cwill713/Software-Defined-Radio/Pictures/Arduino and Si5351.jpg

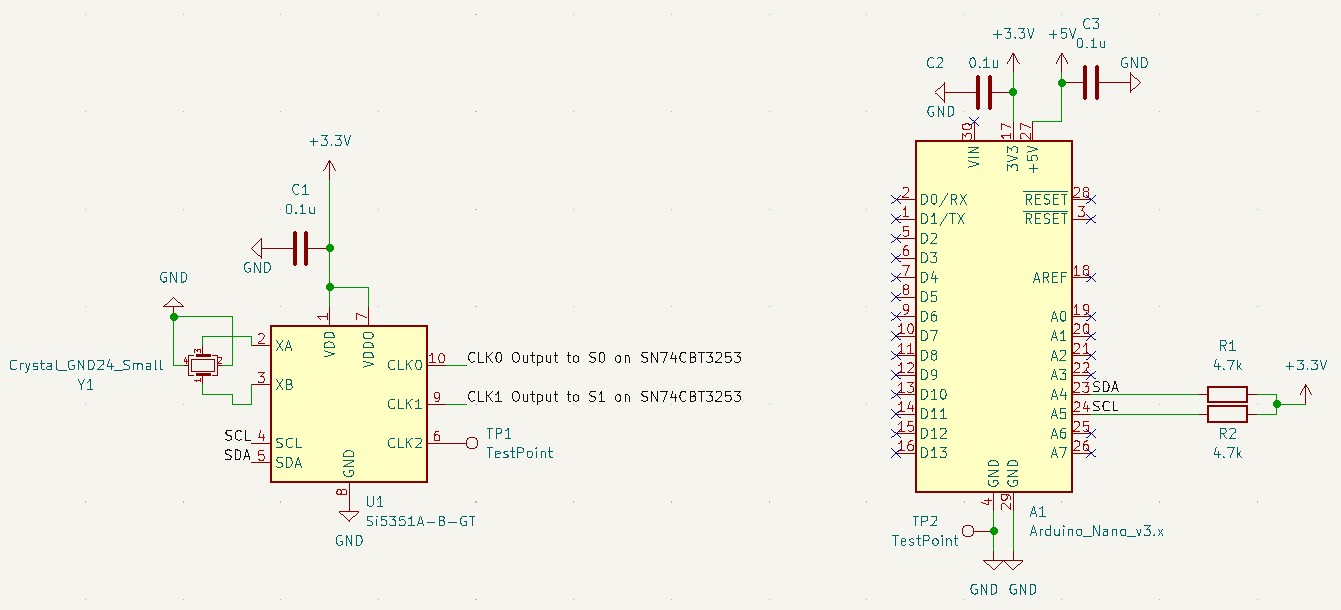
Pictures/Arduino and Si5351.jpg
