cwill713/Software-Defined-Radio/Pictures/BandPass Filter and Voltage Divider.jpg

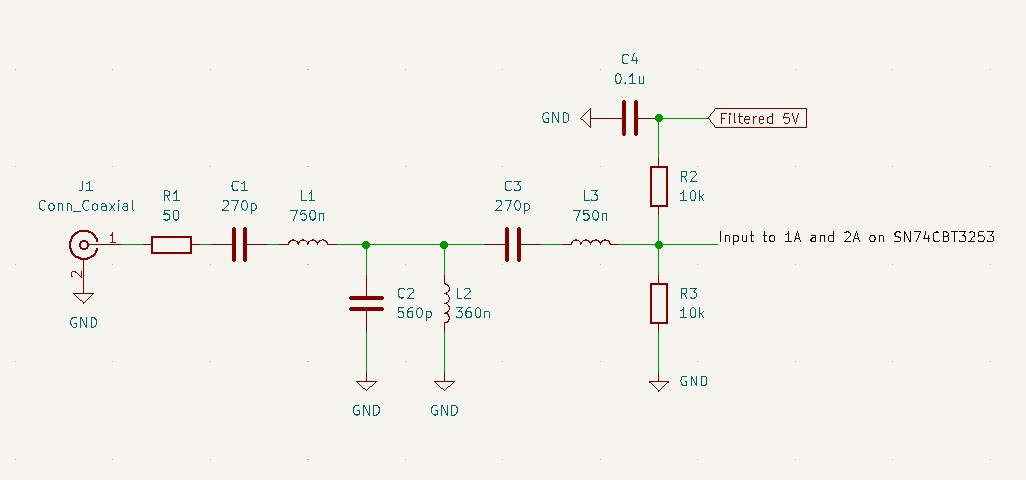
Pictures/BandPass Filter and Voltage Divider.jpg
