cwill713/Software-Defined-Radio/Pictures/Bandpass Filter Simulation Graph.jpg

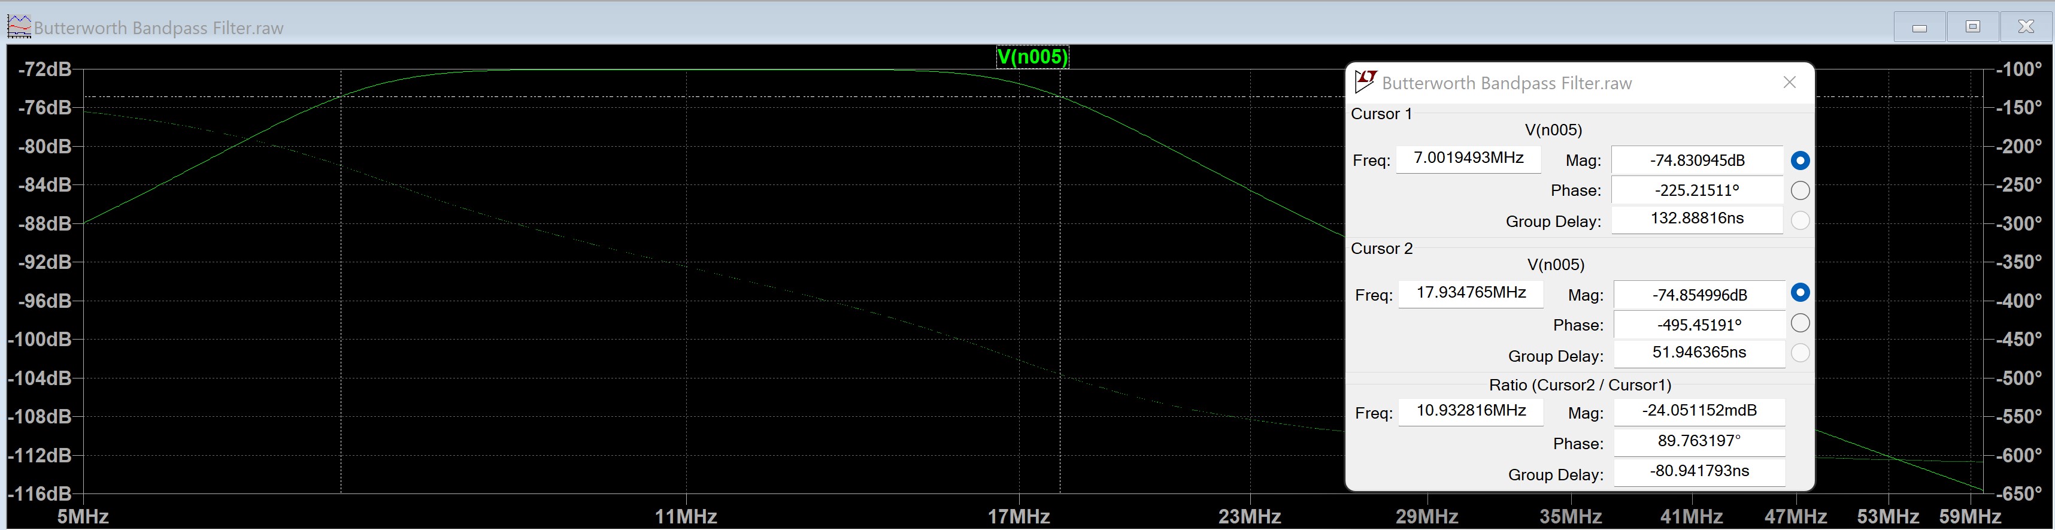
Pictures/Bandpass Filter Simulation Graph.jpg
