cwill713/Software-Defined-Radio/Pictures/Bandpass Filter Simulation.jpg

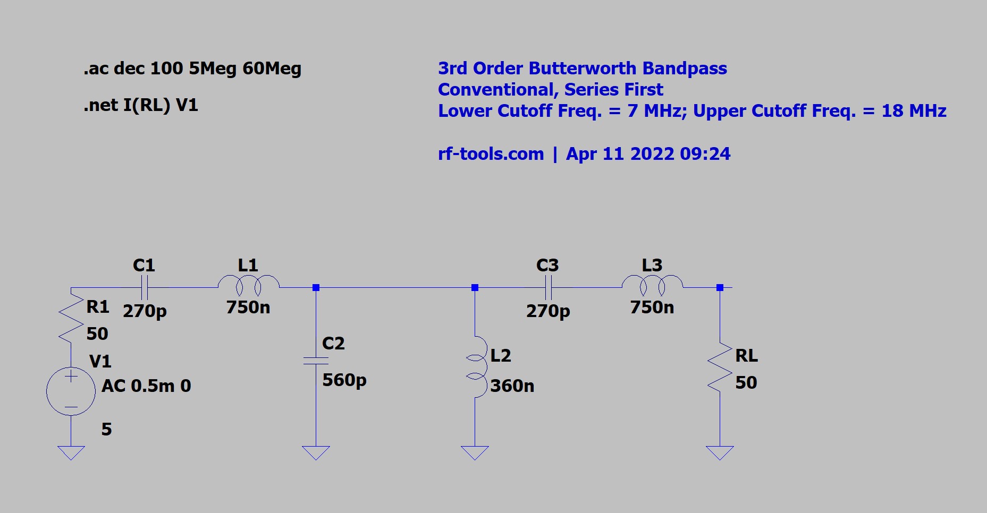
Pictures/Bandpass Filter Simulation.jpg
