cwill713/Software-Defined-Radio/Pictures/Complete SDR Simulation.jpg

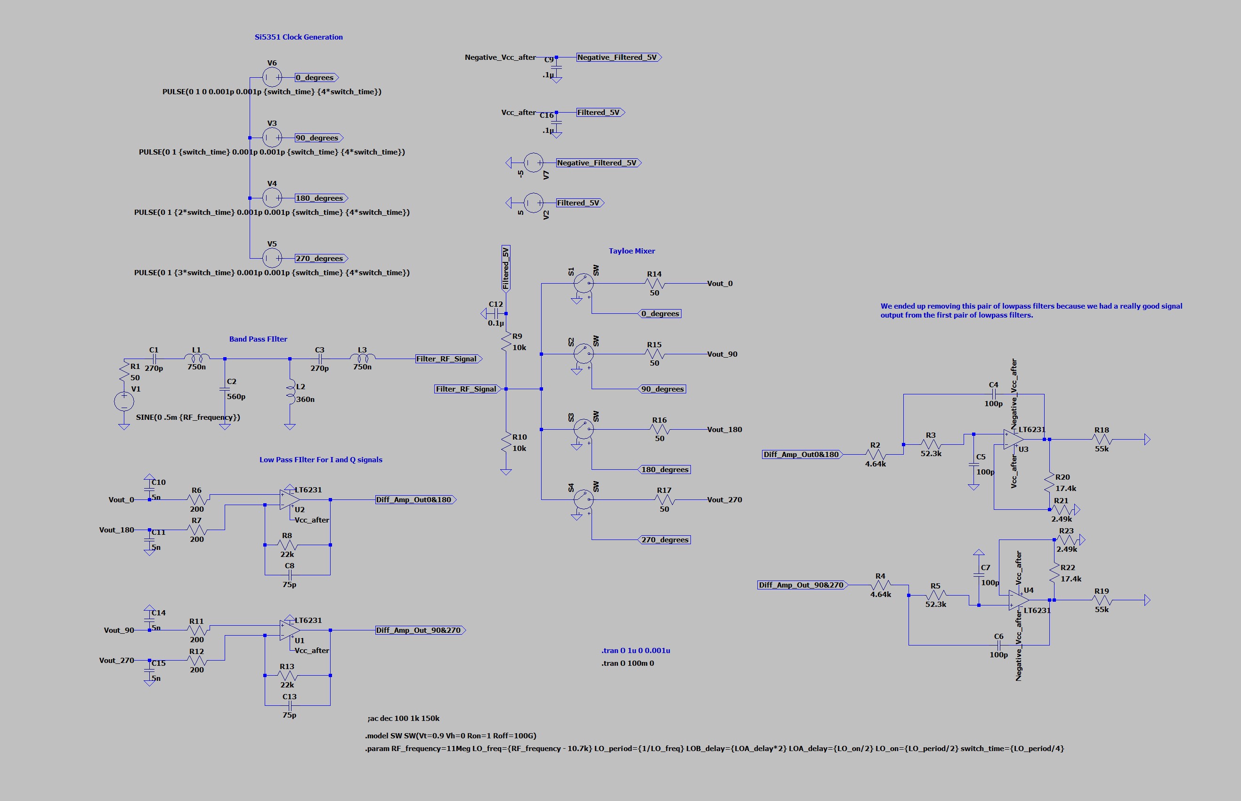
Pictures/Complete SDR Simulation.jpg
