cwill713/Software-Defined-Radio/Pictures/Complete Simulation Graph.jpg

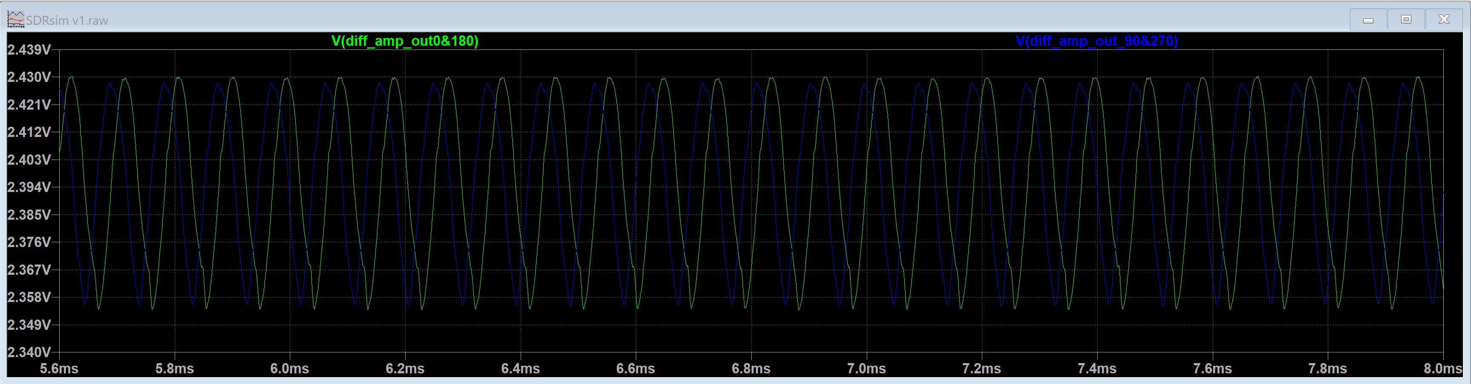
Pictures/Complete Simulation Graph.jpg
