cwill713/Software-Defined-Radio/Pictures/Josh's Fixed Board image 1.jpg

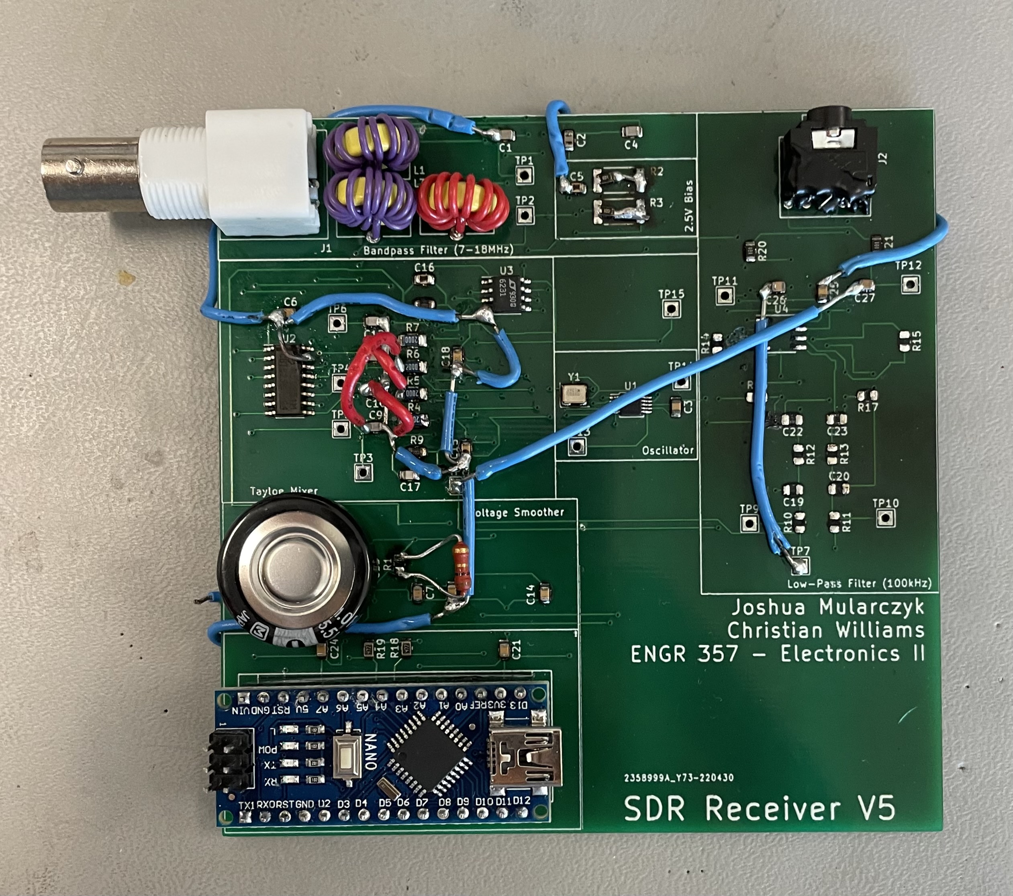
Pictures/Josh's Fixed Board image 1.jpg
