cwill713/Software-Defined-Radio/Pictures/Josh's Fixed Board image 3.jpg

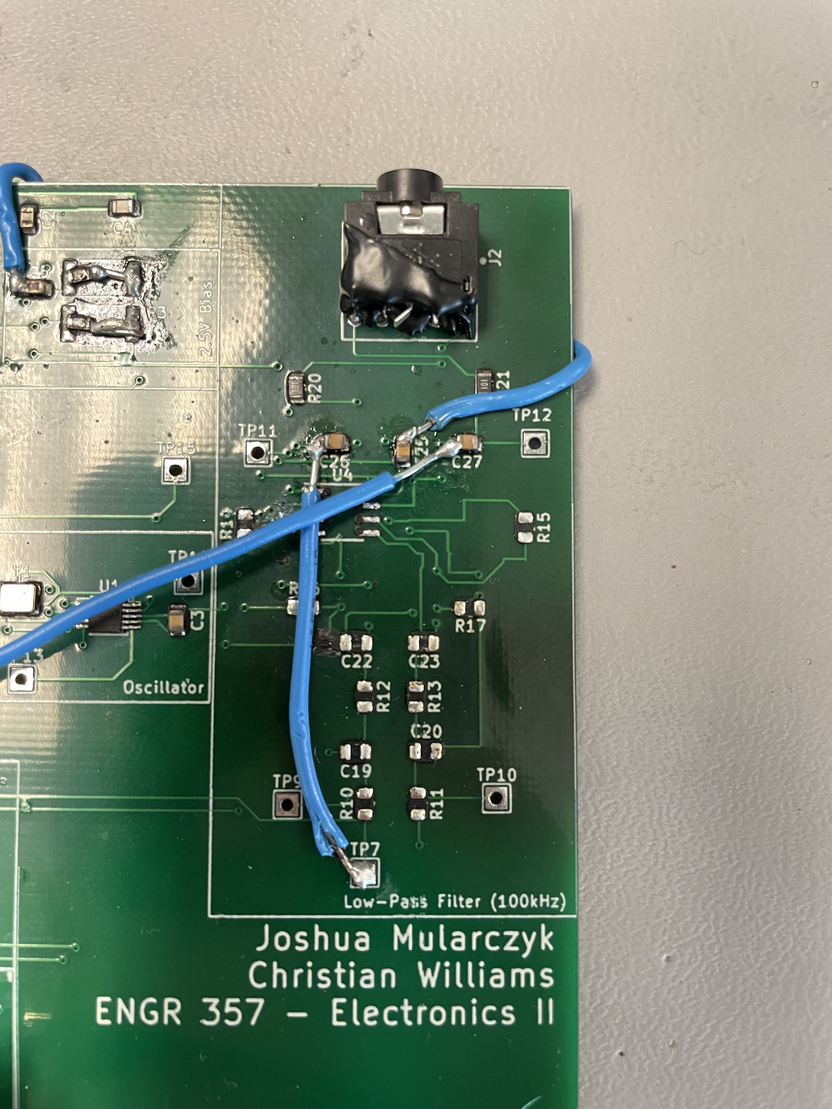
Pictures/Josh's Fixed Board image 3.jpg
