cwill713/Software-Defined-Radio/Pictures/listeningIn.png

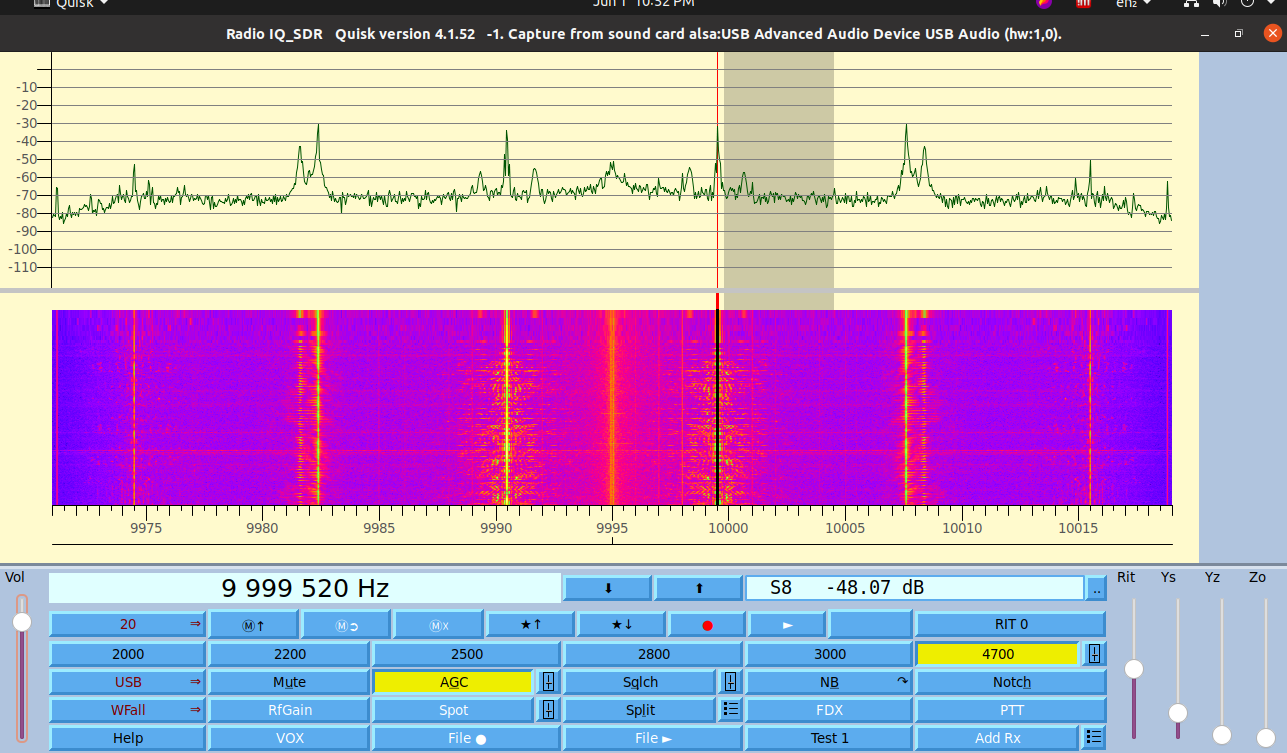
Pictures/listeningIn.png
