cwill713/Software-Defined-Radio/Pictures/LowPass Filter Simulation.jpg

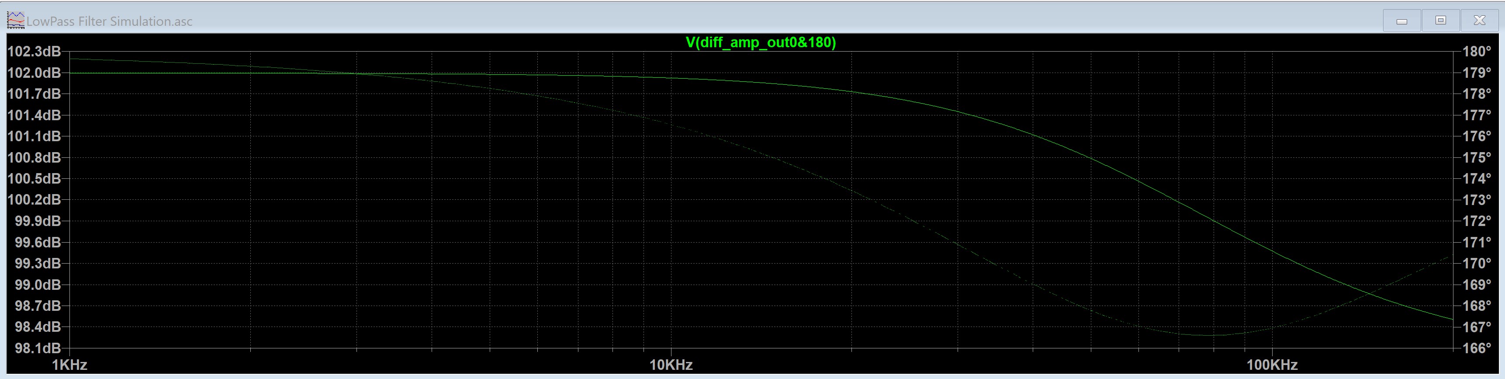
Pictures/LowPass Filter Simulation.jpg
