cwill713/Software-Defined-Radio/Pictures/minDec.png

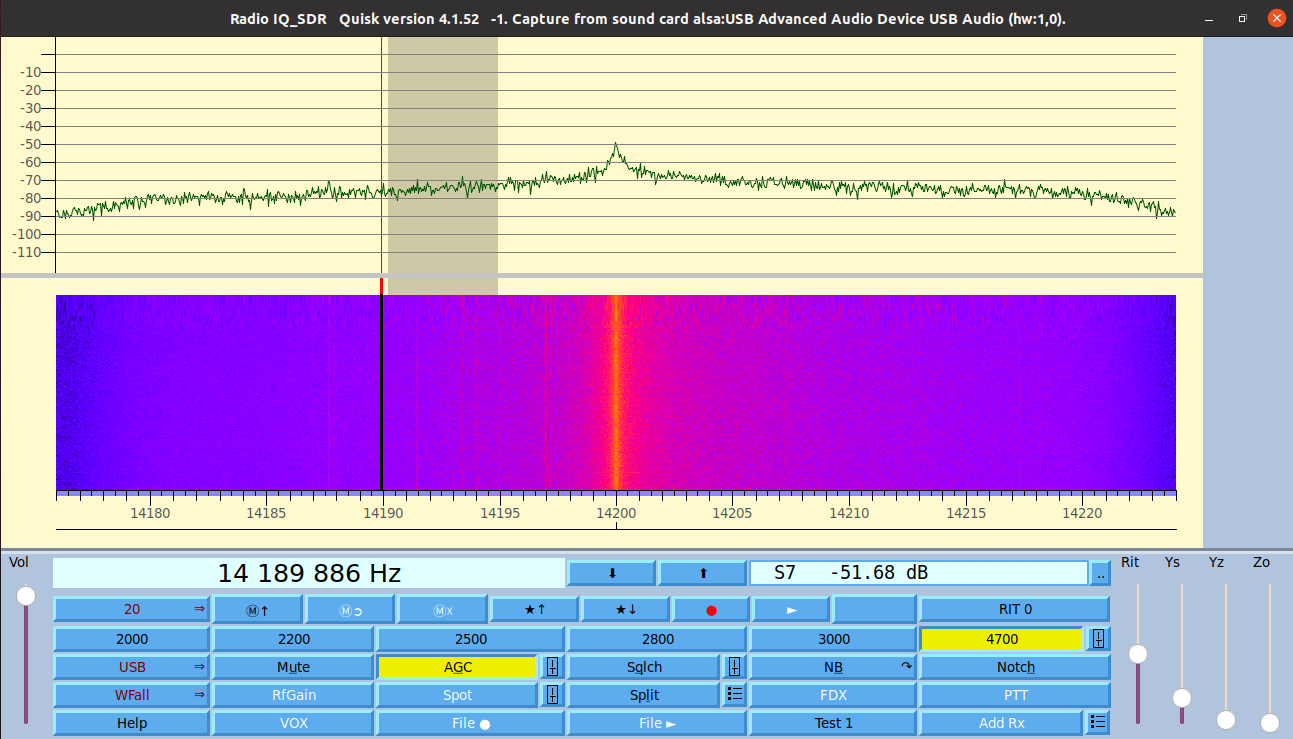
Pictures/minDec.png
