cwill713/Software-Defined-Radio/Pictures/Tayloe Mixer.jpg

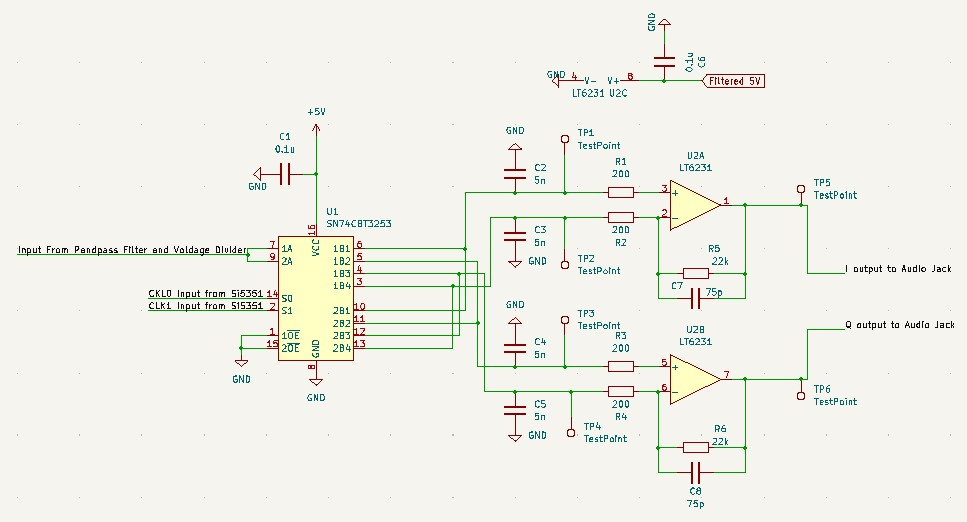
Pictures/Tayloe Mixer.jpg
