cwill713/Software-Defined-Radio/Pictures/V5 Circuit Board.jpg

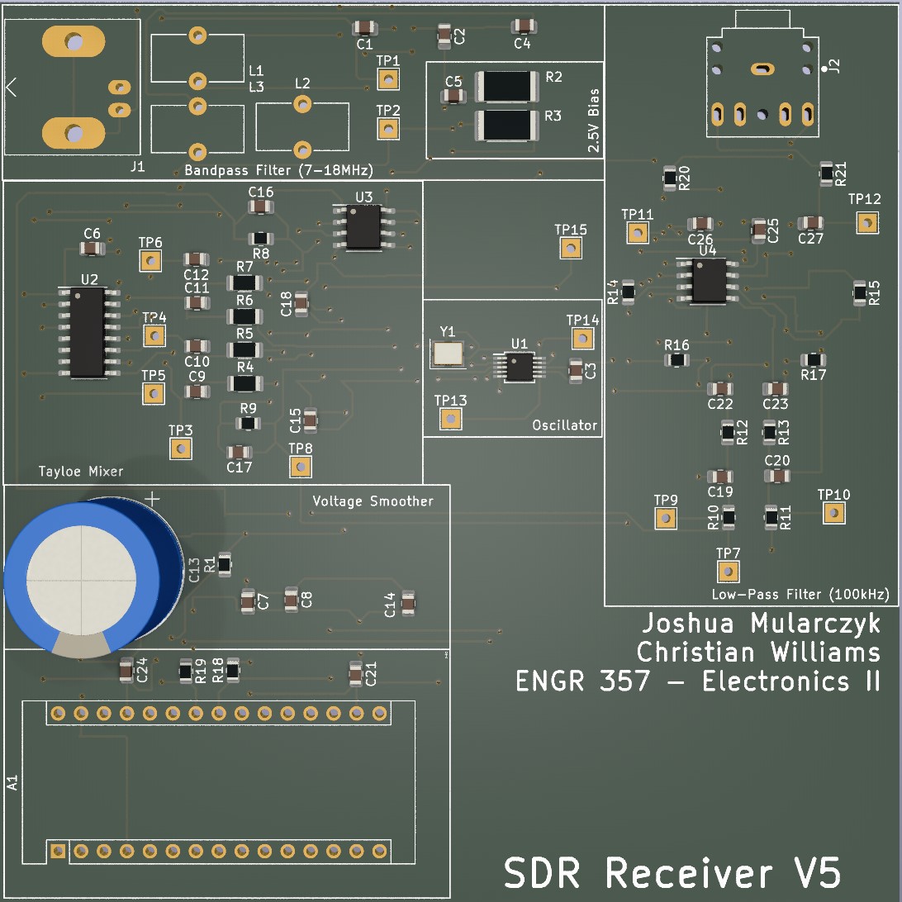
Pictures/V5 Circuit Board.jpg
