cwill713/Software-Defined-Radio/Pictures/Voltage Smoother.jpg

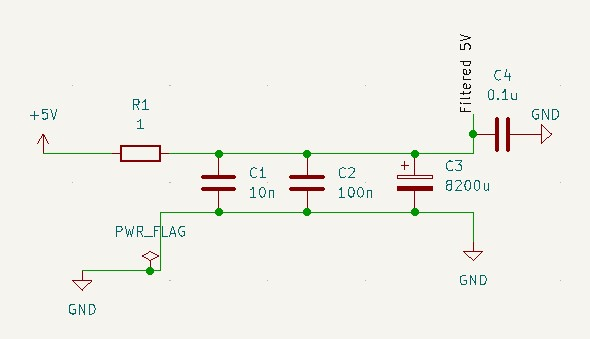
Pictures/Voltage Smoother.jpg
