cwill713/Software-Defined-Radio/Pictures/weather.png

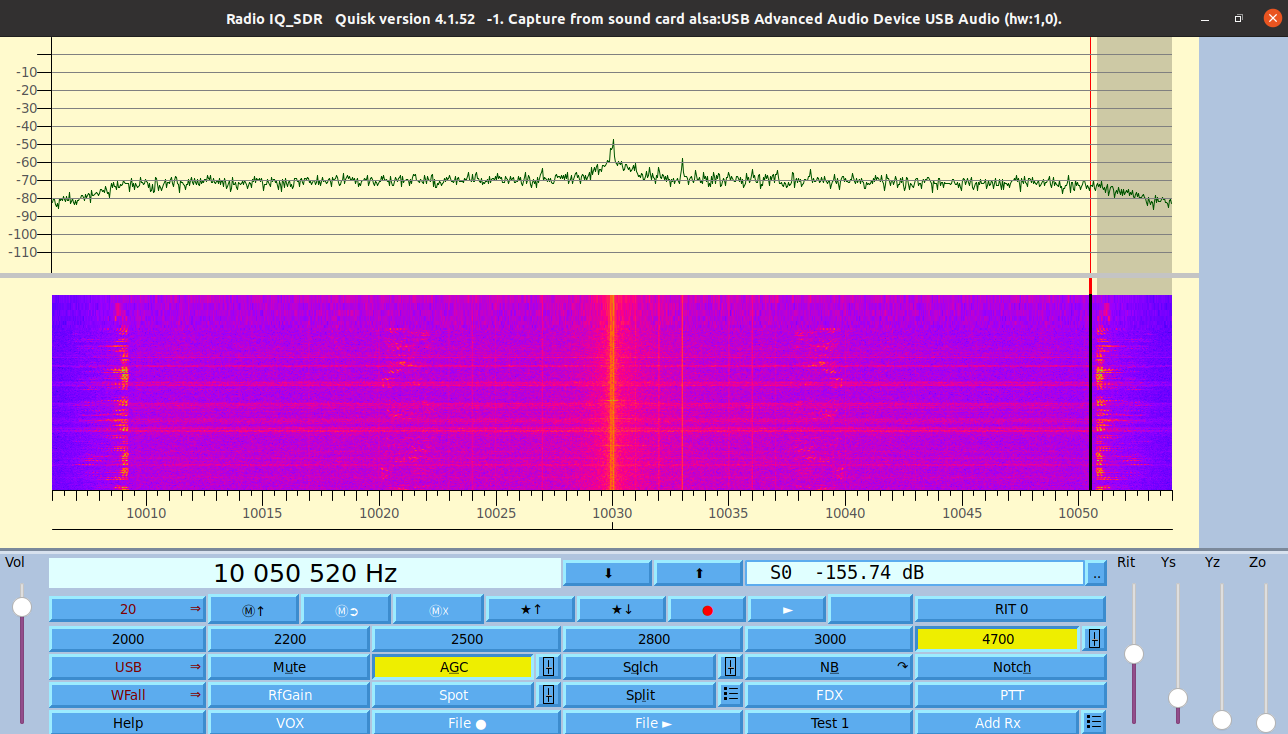
Pictures/weather.png
