cwill713/Software-Defined-Radio/Schematic Files/SDRrecV5/PDFFilesV5/Complete Schematic V4-F_Mask.pdf

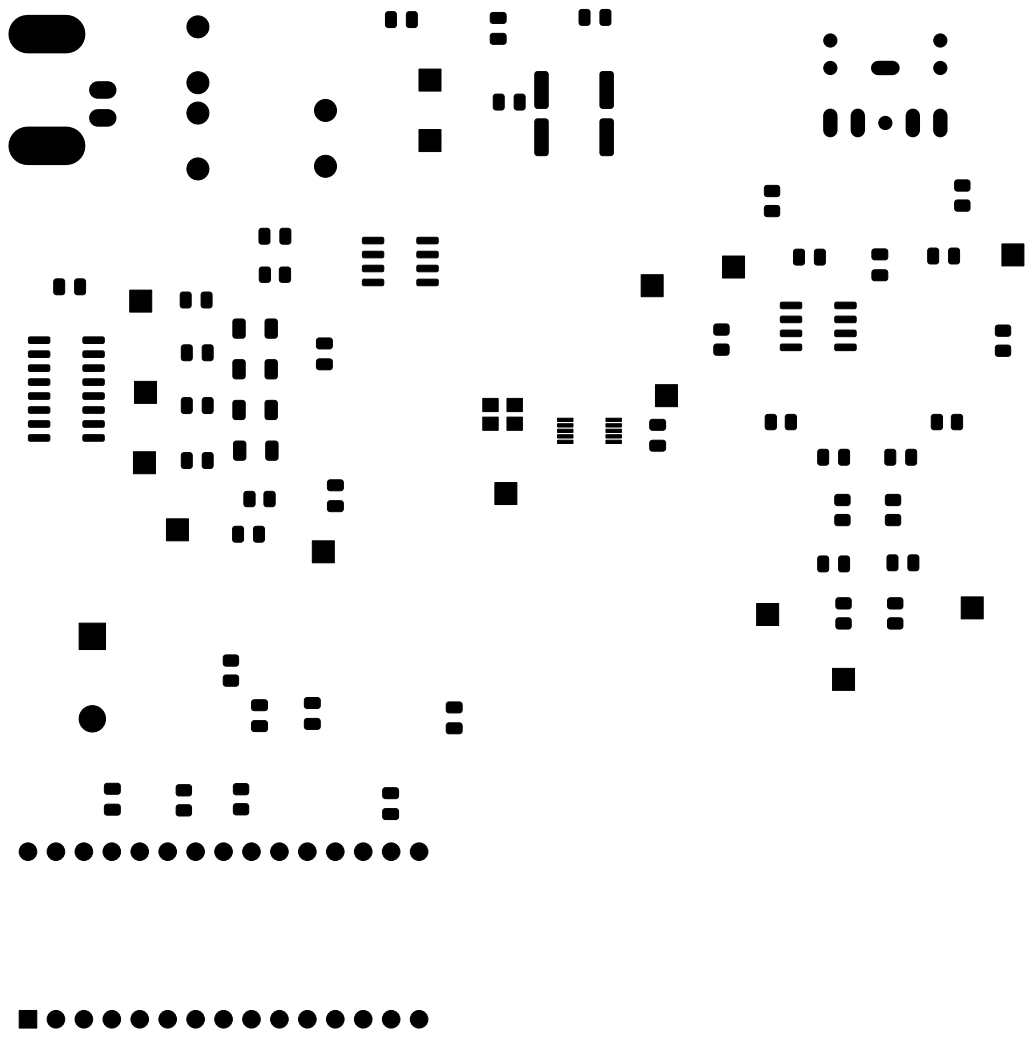
[picture p34: page 1]
