cwill713/Software-Defined-Radio/Schematic Files/SDRrecV5/PDFFilesV5/Complete Schematic V4-F_Silkscreen.pdf

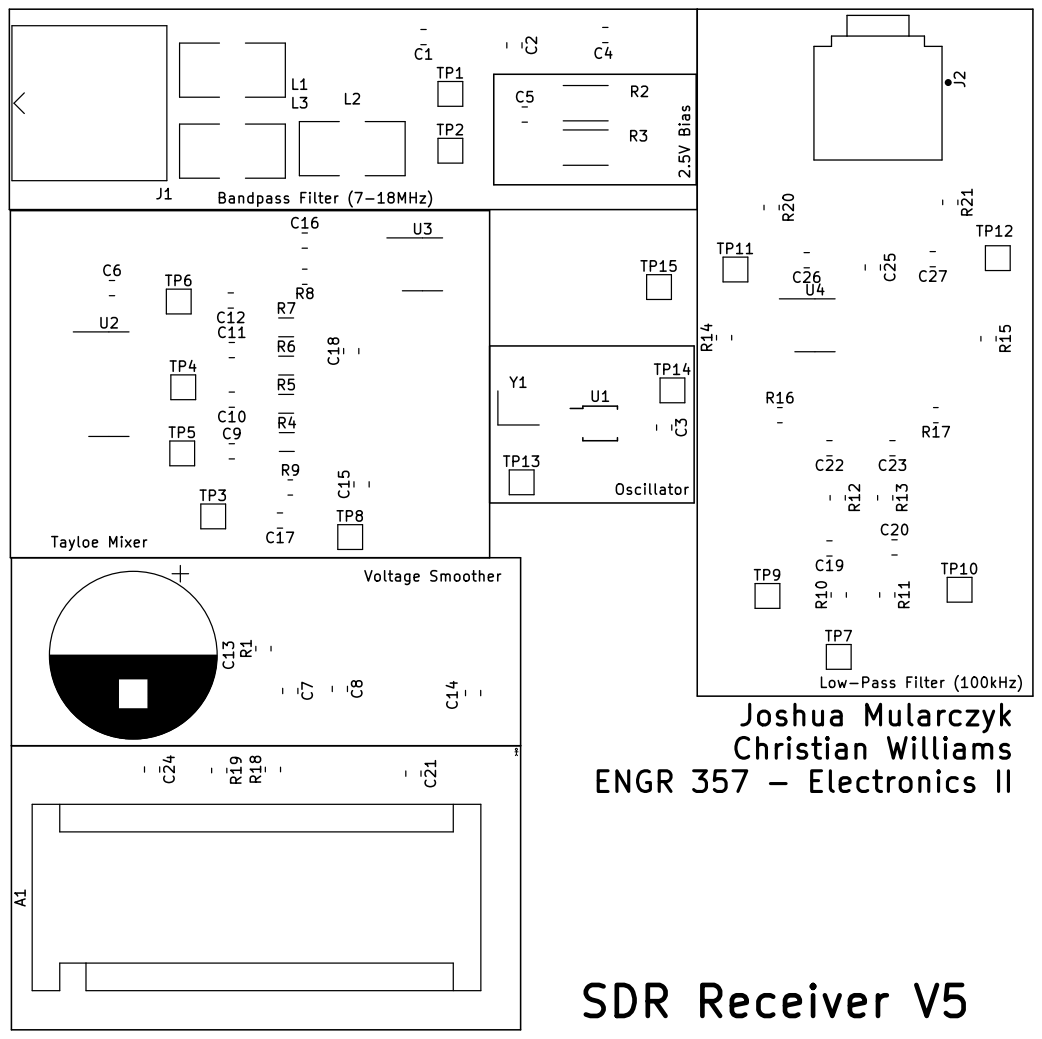
[picture p35: page 1]
