cwill713/Software-Defined-Radio/Simulation Files/LowPass Filter Simulation.asc

C1: cap; 75p
C2: cap; 5n
C3: cap; 5n
R1: res; 200
R2: res; 200
R3: res; 22k
U1: LT6231
V1: voltage; ""; AC 200k 0
V2: voltage; ""; AC 200k 180
Named nets: 0, Vout_0, Vout_180, Vcc_after, Diff_Amp_Out0&180
Low Pass FIlter For I and Q signals
.ac dec 100 1k 200k
