cwill713/Software-Defined-Radio/Simulation Files/Noise Simulation.asc

C1: cap; 5n
C2: cap; 5n
C3: cap; 5n
C4: cap; 75p
C5: cap; 75p
C6: cap; .1µ
C7: cap; 5n
R1: res; 200
R2: res; 200
R3: res; 22k
R4: res; 200
R5: res; 200
R6: res; 22k
R8: res; 55k
R9: res; 10k
R10: res; 50
R11: res; 50
U1: LT6231
U2: LT6231
V1: voltage; 5
V2: voltage; 0
V3: voltage; SINE(0 .5m {RF_frequency})
Named nets: 0, Vout_0, Vout_90, Vout_180, Vout_270, Vcc_after, Diff_Amp_Out_90&270, Diff_Amp_Out0&180, Filtered_5V, Vin
.noise V(Diff_Amp_Out0&180) V3 dec 100 10 100Meg
.param RF_frequency=10Meg LO_freq={RF_frequency - 5.7k} LO_period={1/LO_freq} LOB_delay={LOA_delay*2} LOA_delay={LO_on/2} LO_on={LO_period/2} switch_time={LO_period/4}
