cwill713/Software-Defined-Radio/Schematic/Complete Schematic V4/Complete Schematic V4.kicad_sch

## KiCad design Schematic/Complete Schematic V4/Complete Schematic V4.kicad_sch (2022-04-28)

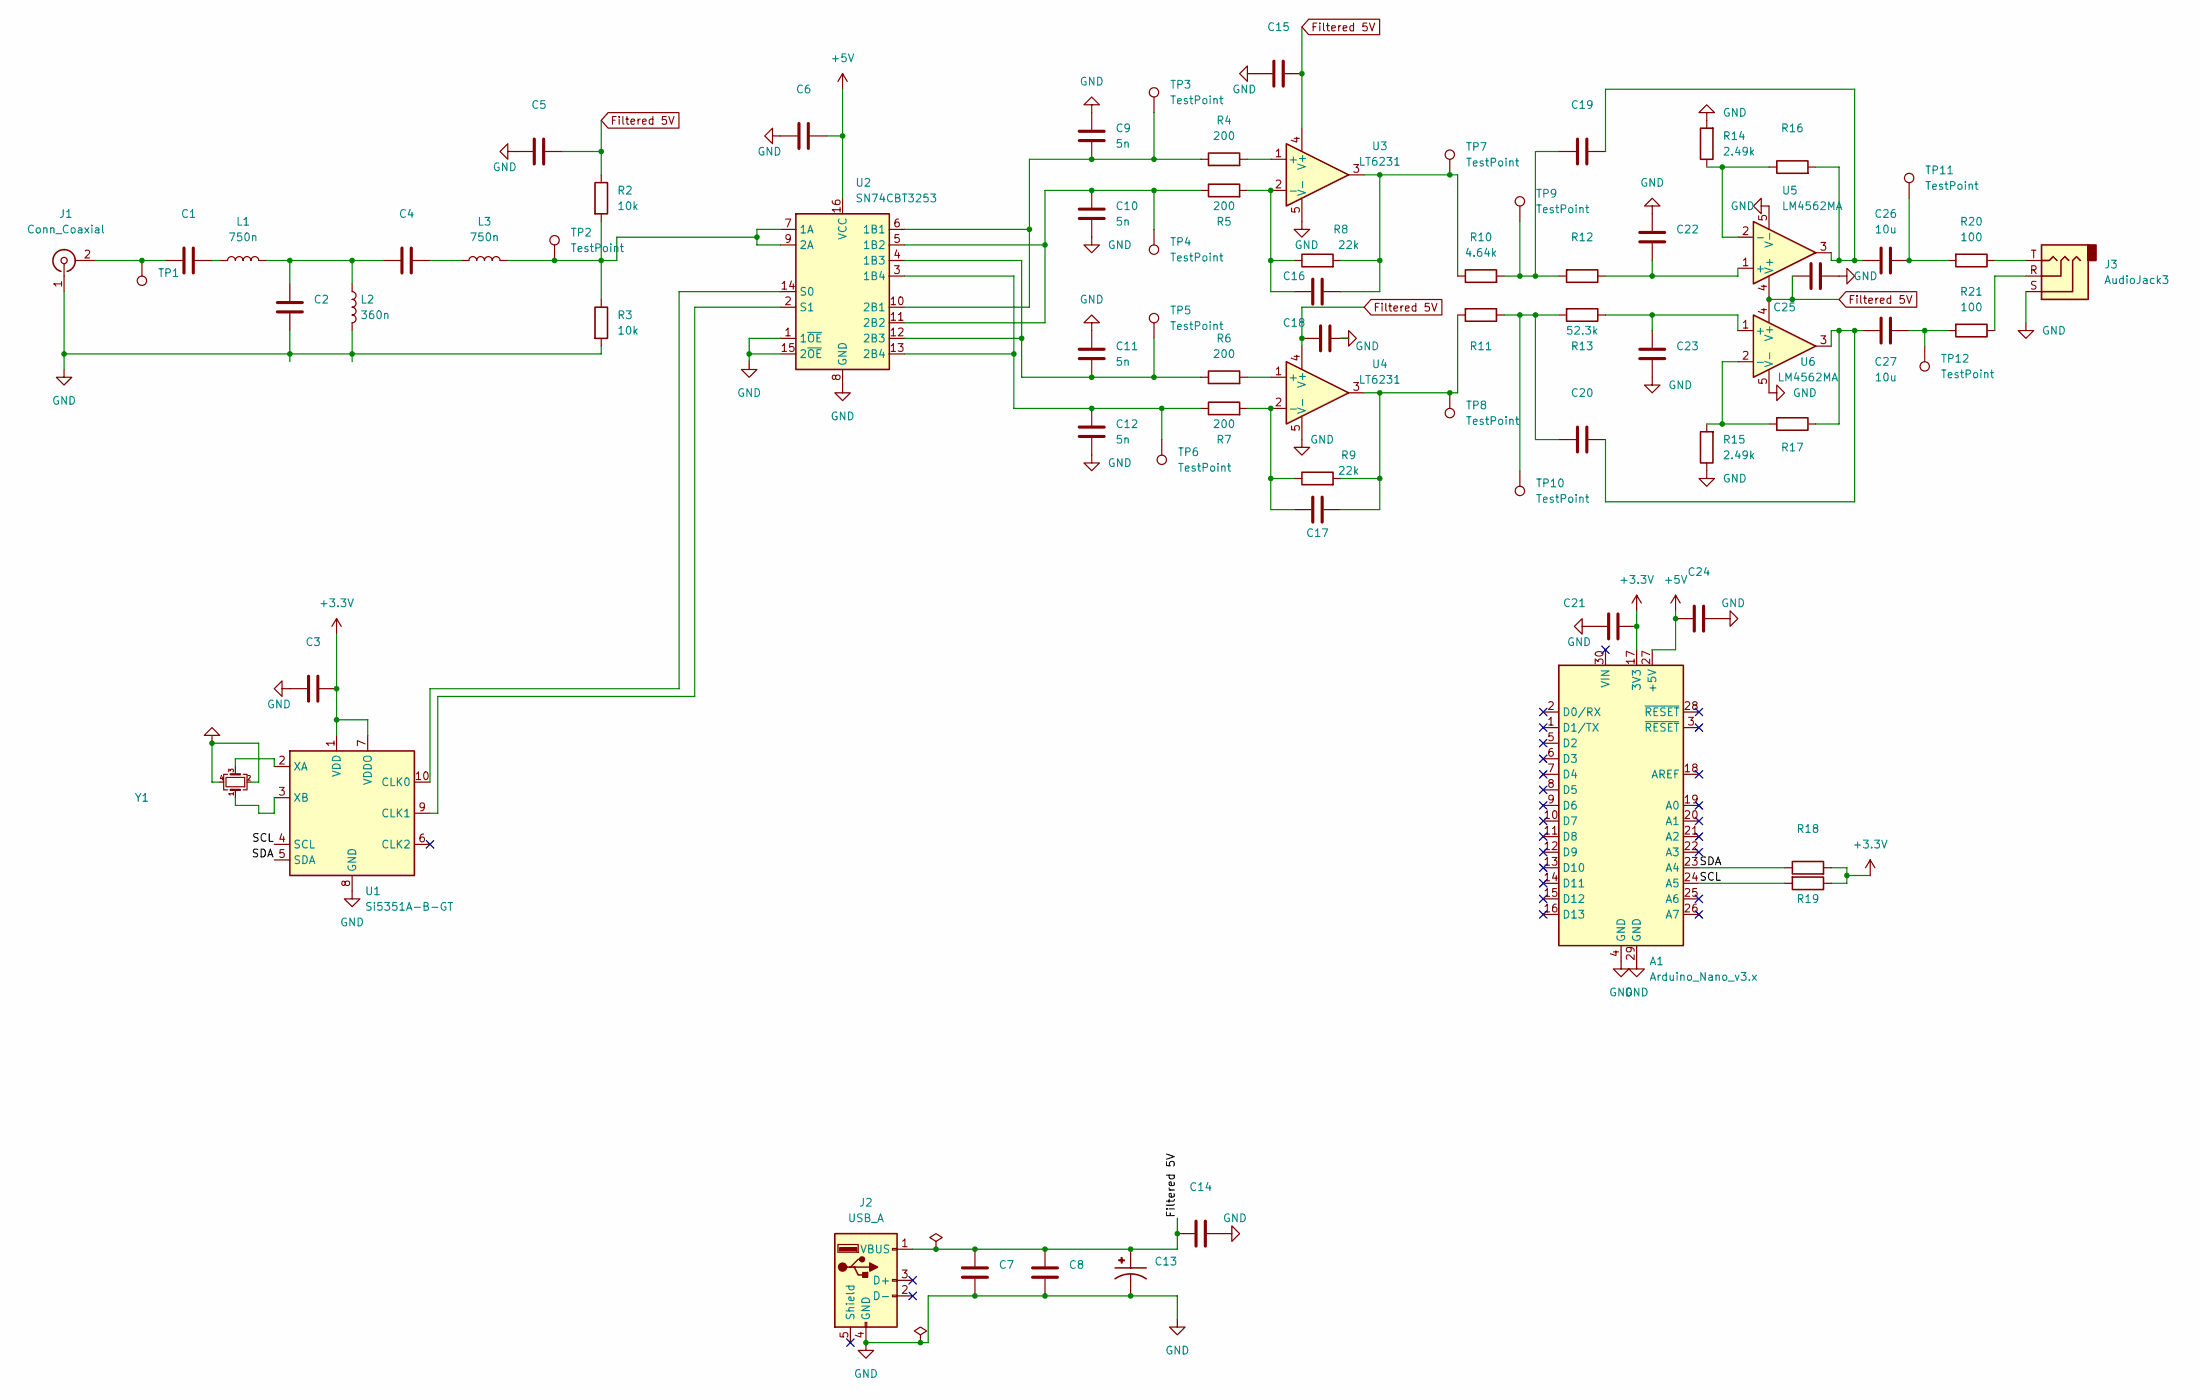
[picture p38: schematic Complete Schematic V4.kicad_sch]

Parts:
A1: Arduino_Nano_v3.x; Arduino_Nano
C1, C2, C3, C4, C5, C6, C7, C8, C14, C15, C16, C17, C18, C19, C20, C21, C22, C23, C24, C25: (no value)
C9, C10, C11, C12: 5n
C13: PARTREV 10-Oct-19
C26, C27: 10u
J1: Conn_Coaxial; BNC_Amphenol_B6252HB-NPP3G-50_Horizontal
J2: USB_A; USB_A_Molex_67643_Horizontal
J3: AudioJack3; Jack_3.5mm_CUI_SJ-3523-SMT_Horizontal
L1: 750n
L2: 360n
L3: 750n; L_0805_2012Metric
R2: 10k
R3: 10k; R_2512_6332Metric
R4, R7: 200; R_1206_3216Metric
R5, R6: 200
R8: 22k
R9: 22k; R_2512_6332Metric
R10: 4.64k
R11, R12, R16, R17, R18, R19: (no value)
R13: 52.3k
R14, R15: 2.49k
R20, R21: 100
TP1: (no value)
TP2, TP3, TP4, TP5, TP6, TP7, TP8, TP9, TP10, TP11, TP12: TestPoint
U1: Si5351A-B-GT; MSOP-10_3x3mm_P0.5mm
U2: SN74CBT3253; SOIC-16_3.9x9.9mm_P1.27mm
U3, U4: LT6231; SOIC-8_3.9x4.9mm_P1.27mm
U5, U6: LM4562MA; SOIC-8_3.9x4.9mm_P1.27mm
Y1: (no value)

Connections:
+3.3V: A1.17 (3V3), C3.2, C21.2, R18.2, R19.1, U1.1 (VDD), U1.7 (VDDO)
+5V: A1.27 (+5V), C6.2, C24.2, U2.16 (VCC)
Filtered 5V: C5.2, C7.1, C8.1, C13.1, C14.2, C15.2, C18.2, C25.2, J2.1 (VBUS), R2.1, U3.4 (V+), U4.4 (V+), U5.4 (V+), U6.4 (V+)
GND: A1.4 (GND), A1.29 (GND), C2.2, C3.1, C5.1, C6.1, C7.2, C8.2, C9.2, C10.1, C11.2, C12.1, C13.2, C14.1, C15.1, C18.1, C21.1, C22.2, C23.1, C24.1, C25.1, J1.1 (In), J2.4 (GND), J3.S, L2.2, R3.2, R14.2, R15.1, U1.8 (GND), U2.1 (1~OE), U2.8 (GND), U2.15 (2~OE), U3.5 (V-), U4.5 (V-), U5.5 (V-), U6.5 (V-)
unnamed: C1.1, L1.1
unnamed: C1.2, J1.2 (Ext), TP1.1
unnamed: C2.1, C4.1, L1.2, L2.1
unnamed: C4.2, L3.1
unnamed: C9.1, R4.1, TP3.1, U2.6 (1B1), U2.10 (2B1)
unnamed: C10.2, R5.1, TP4.1, U2.5 (1B2), U2.11 (2B2)
unnamed: C11.1, R6.1, TP5.1, U2.4 (1B3), U2.12 (2B3)
unnamed: C12.2, R7.1, TP6.1, U2.3 (1B4), U2.13 (2B4)
unnamed: C16.1, R8.2, R10.1, TP7.1, U3.3
unnamed: C16.2, R5.2, R8.1, U3.2 (-)
unnamed: C17.1, R9.2, R11.2, TP8.1, U4.3
unnamed: C17.2, R7.2, R9.1, U4.2 (-)
unnamed: C19.1, R10.2, R12.2, TP9.1
unnamed: C19.2, C26.2, R16.2, U5.3
unnamed: C20.1, R11.1, R13.2, TP10.1
unnamed: C20.2, C27.2, R17.1, U6.3
unnamed: C22.1, R12.1, U5.1 (+)
unnamed: C23.2, R13.1, U6.1 (+)
unnamed: C26.1, R20.2, TP11.1
unnamed: C27.1, R21.2, TP12.1
unnamed: J3.R, R21.1
unnamed: J3.T, R20.1
unnamed: L3.2, R2.2, R3.1, TP2.1, U2.7 (1A), U2.9 (2A)
unnamed: R4.2, U3.1 (+)
unnamed: R6.2, U4.1 (+)
unnamed: R14.1, R16.1, U5.2 (-)
unnamed: R15.2, R17.2, U6.2 (-)
unnamed: U1.2 (XA), Y1.3
unnamed: U1.3 (XB), Y1.1
unnamed: U1.9 (CLK1), U2.2 (S1)
unnamed: U1.10 (CLK0), U2.14 (S0)
unnamed: Y1.2, Y1.4
SCL: A1.24 (A5), R19.2, U1.4 (SCL)
SDA: A1.23 (A4), R18.1, U1.5 (SDA)
