cwill713/Software-Defined-Radio/Pictures/Christian's Fixed Board Post Mistake img 2.jpg

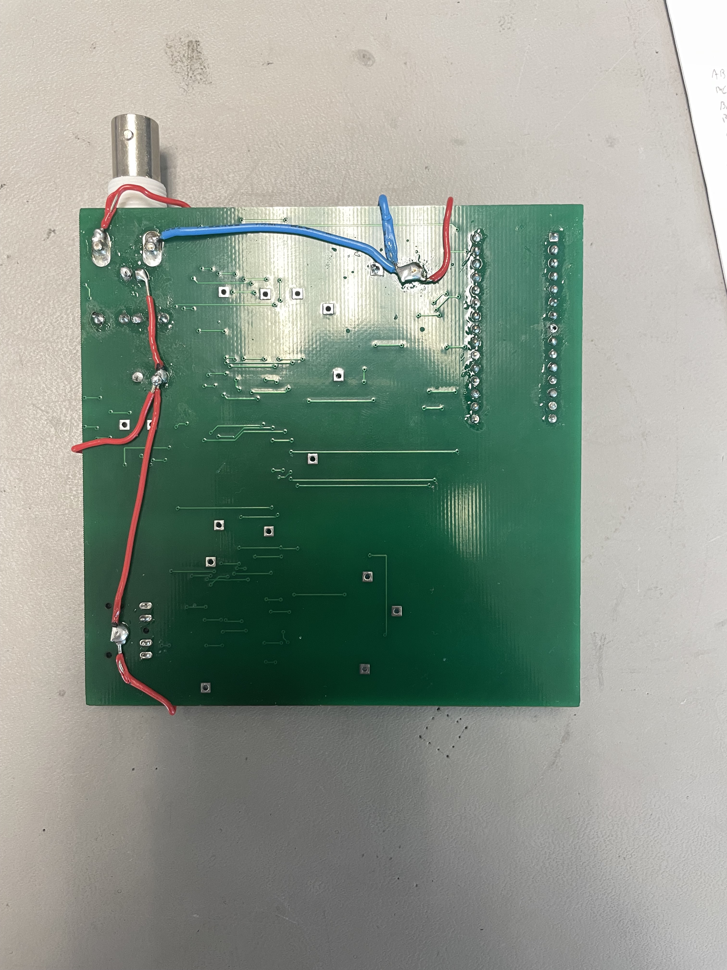
Pictures/Christian's Fixed Board Post Mistake img 2.jpg
