cwill713/Software-Defined-Radio/Pictures/Christian's Fixed Board Post Mistake.jpg

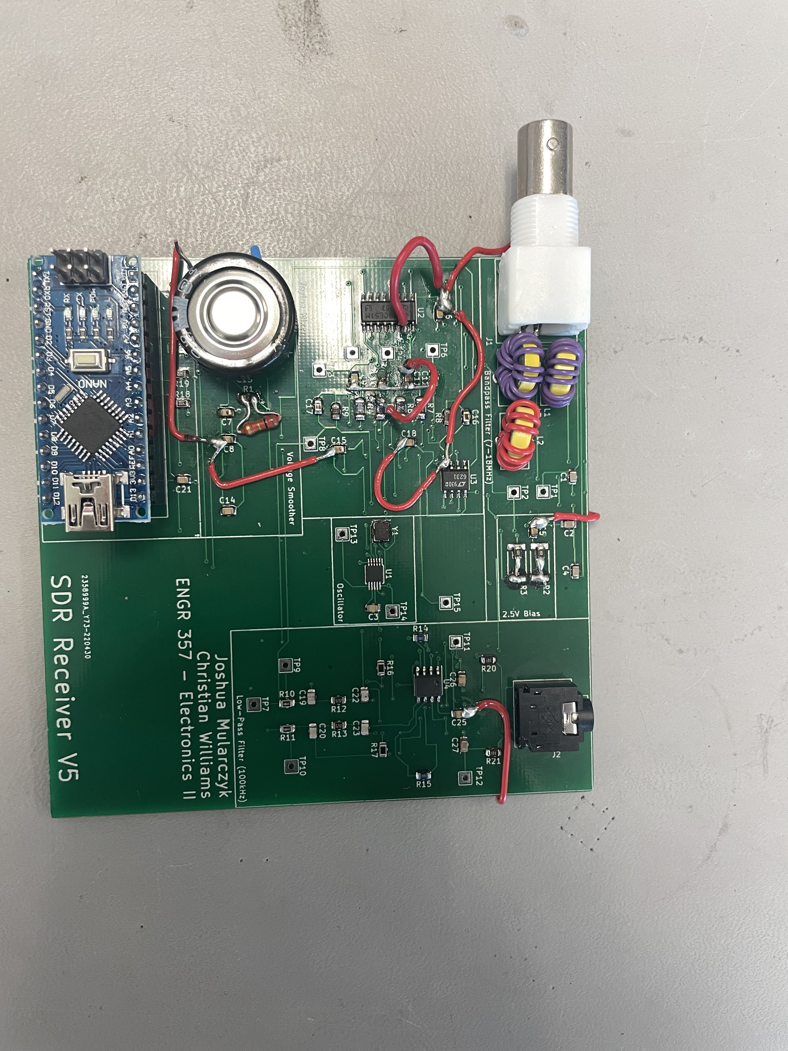
Pictures/Christian's Fixed Board Post Mistake.jpg
